likeablob/slow-movie-player-7c/openscad/smp7c_spacer_01_top_left.scad

include <modules/smp7c_spacer.scad>

$fn=50;

EDGE_POS=0;

rotate([180, 0, 180])
smp7c_spacer_body_at(edge_pos=EDGE_POS);
