likeablob/slow-movie-player-7c/openscad/smp7c_spacer_02_top_right.scad

include <./smp7c_spacer_01_top_left.scad>

EDGE_POS=1;
