likeablob/slow-movie-player-7c/openscad/smp7c_spacer_04_bottom_left.scad

include <./smp7c_spacer_01_top_left.scad>

EDGE_POS=3;
