likeablob/slow-movie-player-7c/ulp/ulp_main.h

// Variable definitions for ESP32ULP
// This file is generated automatically by esp32ulp_mapgen.py utility

#pragma once

extern uint32_t ulp__counterPeriodicTask;
extern uint32_t ulp_entry;
extern uint32_t ulp_epdBusyStatus;
extern uint32_t ulp_status;
