likeablob/slow-movie-player-7c/ulp/ulp_common.h

// This header is shared between the main program and ULP.
// Therefore it should only contain "plain" values.
#define COUNTER_PERIODIC_TASK 3600 // Wake up period. 3600 sec = 1 hour

#define PM_STATUS_WAIT_BUSY_REQ 0x1
#define PM_STATUS_WAIT_BUSY_REQ_M 0xFFFE
#define PM_STATUS_FOREVER_SLEEP_REQ 0x2
